joulupukki/q-tune/font-images/tuner_font_image_b2x.png

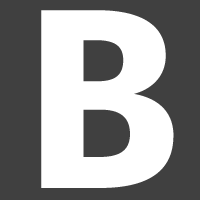
font-images/tuner_font_image_b2x.png
