joulupukki/q-tune/font-images/tuner_font_image_e2x.png

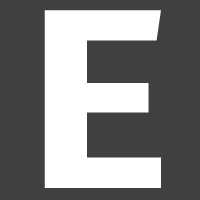
font-images/tuner_font_image_e2x.png
