joulupukki/q-tune/main/waveshare/LVGL_Driver.h

#pragma once
#include <stdio.h>
#include "freertos/FreeRTOS.h"
#include "freertos/task.h"
#include "esp_timer.h"
#include "esp_err.h"
#include "esp_log.h"
#include "lvgl.h"

#include "ST7789.h"

#define LVGL_BUF_LEN  (LCD_H_RES * LCD_V_RES / 10)
#define LVGL_TICK_PERIOD_MS    2

// extern lv_disp_draw_buf_t disp_buf;                                                 // contains internal graphic buffer(s) called draw buffer(s)
// extern lv_disp_drv_t disp_drv;                                                      // contains callback functions
// extern lv_disp_t *disp;    

bool lvgl_notify_lvgl_flush_ready(esp_lcd_panel_io_handle_t panel_io, esp_lcd_panel_io_event_data_t *edata, void *user_ctx);
void lvgl_flush_cb(lv_display_t *display, const lv_area_t *area, uint8_t * px_map);
/* Rotate display and touch, when rotated screen in LVGL. Called when driver parameters are updated. */
// void lvgl_port_update_callback(lv_disp_drv_t *drv);
void increase_lvgl_tick(void *arg);

void LVGL_Init(void);                     // Call this function to initialize the screen (must be called in the main function) !!!!!
