joulupukki/q-tune/main/waveshare/ST7789.c

#include "ST7789.h"

#include <esp_check.h>
#include "defines.h"

static const char *TAG = "ST7789";

extern esp_lcd_panel_io_handle_t lcd_io;
extern esp_lcd_panel_handle_t lcd_panel;

esp_err_t LCD_Init(void)
{
    ESP_LOGI(TAG, "Initialize SPI bus");                                            
    spi_bus_config_t buscfg = {                                                         
        .sclk_io_num = PIN_NUM_SCLK,                                            
        .mosi_io_num = PIN_NUM_MOSI,                                            
        .miso_io_num = PIN_NUM_MISO,                                            
        .quadwp_io_num = -1,                                                            
        .quadhd_io_num = -1,                                                            
        .max_transfer_sz = LCD_DRAWBUF_SIZE * sizeof(uint16_t),    
    };
    ESP_RETURN_ON_ERROR(spi_bus_initialize(LCD_HOST, &buscfg, SPI_DMA_CH_AUTO), TAG, "SPI init failed");

    ESP_LOGI(TAG, "Install panel IO");
    esp_lcd_panel_io_spi_config_t io_config = {                                             
        .dc_gpio_num = PIN_NUM_LCD_DC,
        .cs_gpio_num = PIN_NUM_LCD_CS,
        .pclk_hz = LCD_PIXEL_CLOCK_HZ,
        .lcd_cmd_bits = LCD_CMD_BITS,
        .lcd_param_bits = LCD_PARAM_BITS,
        .spi_mode = 0,
        .trans_queue_depth = 10,
    };
    // Attach the LCD to the SPI bus
    ESP_ERROR_CHECK(esp_lcd_new_panel_io_spi((esp_lcd_spi_bus_handle_t)LCD_HOST, &io_config, &lcd_io));

    esp_lcd_panel_dev_st7789t_config_t panel_config = {
        .reset_gpio_num = PIN_NUM_LCD_RST,
        .rgb_endian = LCD_RGB_ENDIAN_BGR,
        .bits_per_pixel = 16,
    };
    ESP_RETURN_ON_ERROR(esp_lcd_new_panel_st7789t(lcd_io, &panel_config, &lcd_panel), TAG, "Failed to create new ST7789T panel");

    ESP_ERROR_CHECK(esp_lcd_panel_reset(lcd_panel));
    ESP_ERROR_CHECK(esp_lcd_panel_init(lcd_panel));
    ESP_ERROR_CHECK(esp_lcd_panel_mirror(lcd_panel, true, false));
    ESP_ERROR_CHECK(esp_lcd_panel_disp_on_off(lcd_panel, true));

    ESP_LOGI(TAG, "Turn on LCD backlight");
    // gpio_set_level(PIN_NUM_BK_LIGHT, LCD_BK_LIGHT_ON_LEVEL);
    
    Backlight_Init();    
    TOUCH_Init();

    return ESP_OK;
}

//////////////////////////////////////////////////////////////////////////////////////////////////////////////////////////////////////////////////////////////////////////////////////////////////////////////////////////////////////////////
// Backlight program

uint8_t LCD_Backlight = 70;
static ledc_channel_config_t ledc_channel;
void Backlight_Init(void)
{
    ESP_LOGI(TAG, "Turn off LCD backlight");
    gpio_config_t bk_gpio_config = {
        .mode = GPIO_MODE_OUTPUT,
        .pin_bit_mask = 1ULL << PIN_NUM_BK_LIGHT
    };
    ESP_ERROR_CHECK(gpio_config(&bk_gpio_config));

    ledc_timer_config_t ledc_timer = {
        // .duty_resolution = LEDC_TIMER_13_BIT, // Waveshare original
        .duty_resolution = LEDC_TIMER_10_BIT, // Lower to allow a faster freq_hz
        // .freq_hz = 5000, // Waveshare original
        .freq_hz = 30000, // Required to get the noise out of the human hearing range
        .speed_mode = LEDC_LS_MODE,
        .timer_num = LEDC_HS_TIMER,
        .clk_cfg = LEDC_AUTO_CLK
    };
    ledc_timer_config(&ledc_timer);

    ledc_channel.channel    = LEDC_HS_CH0_CHANNEL;
    ledc_channel.duty       = 0;
    ledc_channel.gpio_num   = PIN_NUM_BK_LIGHT;
    ledc_channel.speed_mode = LEDC_LS_MODE;
    ledc_channel.timer_sel  = LEDC_HS_TIMER;
    ledc_channel_config(&ledc_channel);
    ledc_fade_func_install(0);
    
    Set_Backlight(LCD_Backlight);      //0~100    
}
void Set_Backlight(uint8_t Light)
{   
    if(Light > Backlight_MAX) Light = Backlight_MAX;
    uint32_t duty = Light * (1024 / 100);
    ledc_set_duty(ledc_channel.speed_mode, ledc_channel.channel, duty);
    ledc_update_duty(ledc_channel.speed_mode, ledc_channel.channel);
}
// end Backlight program
